gitzense/locker/pics/billet_2.jpg

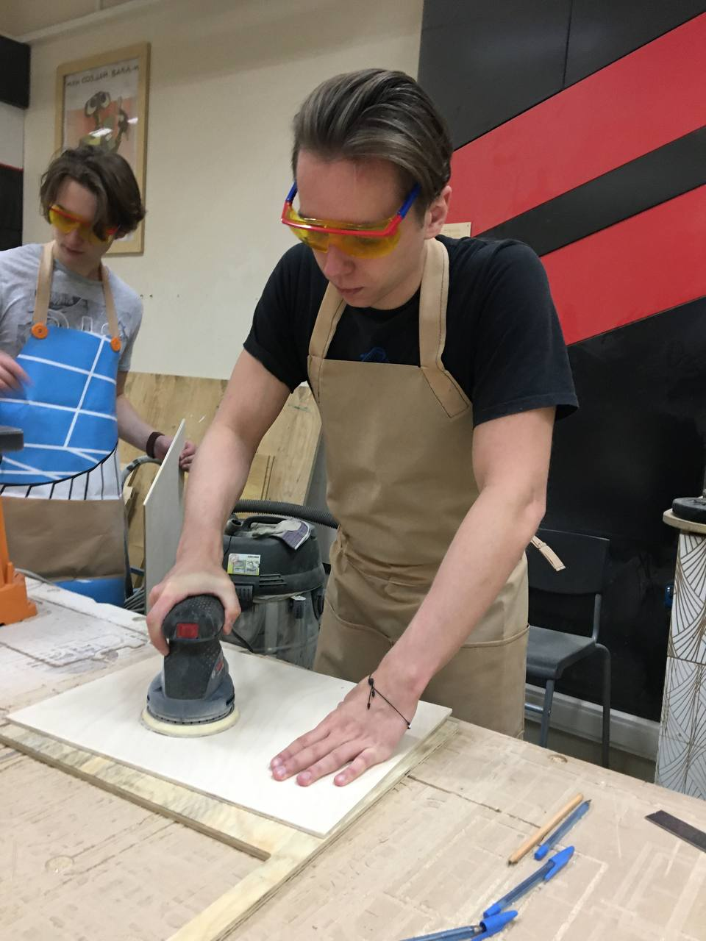
pics/billet_2.jpg
