gitzense/locker/pics/billet_3.jpg

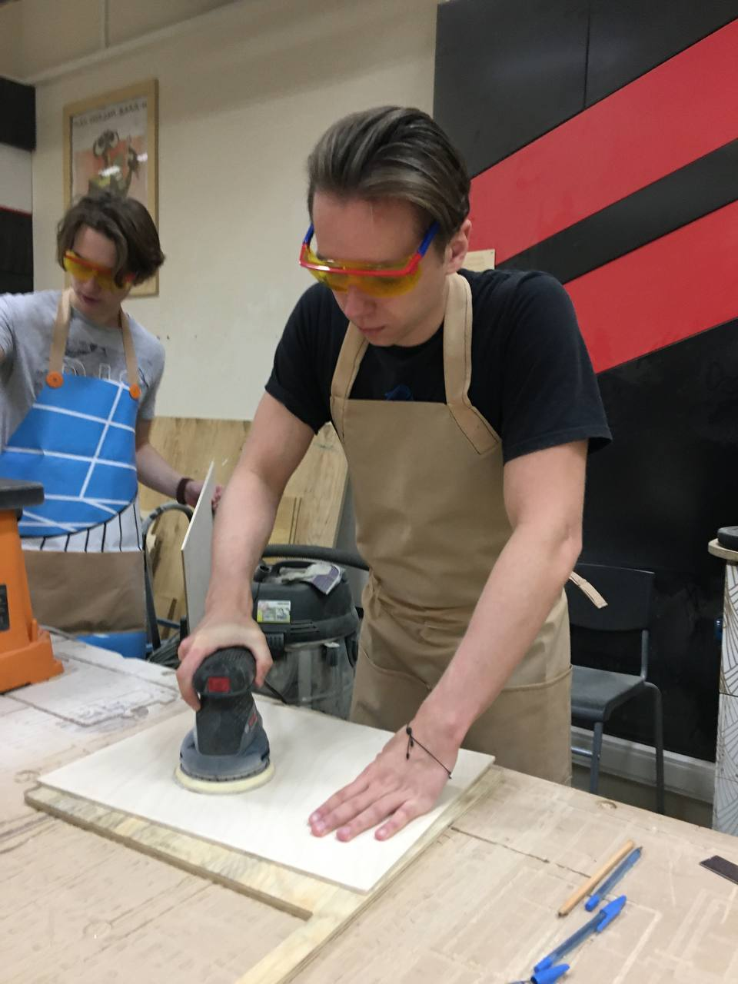
pics/billet_3.jpg
