gitzense/locker/pics/billet_4.jpg

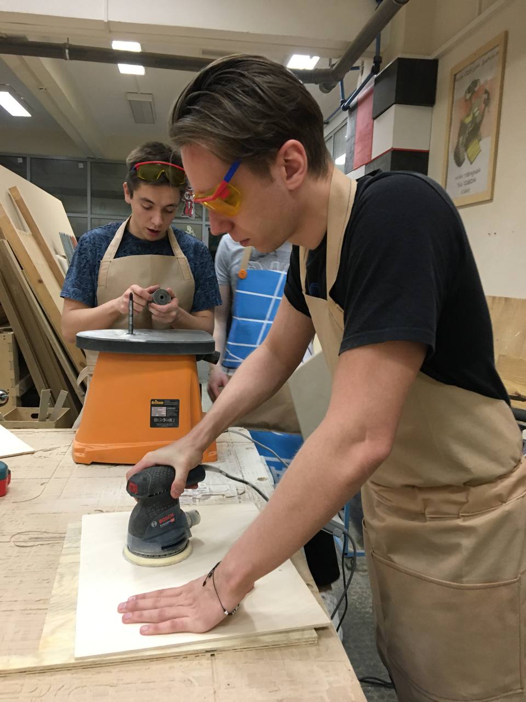
pics/billet_4.jpg
