gitzense/locker/pics/billet_5.jpg

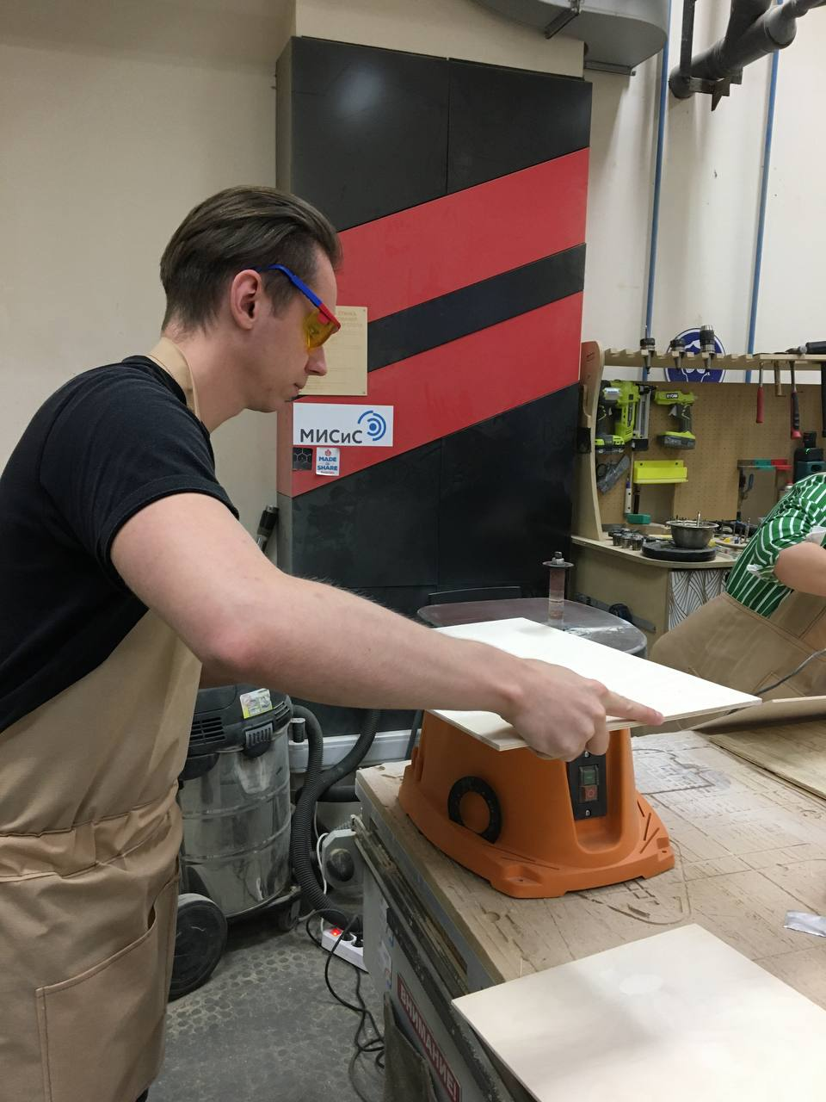
pics/billet_5.jpg
