gitzense/locker/pics/billet_7.jpg

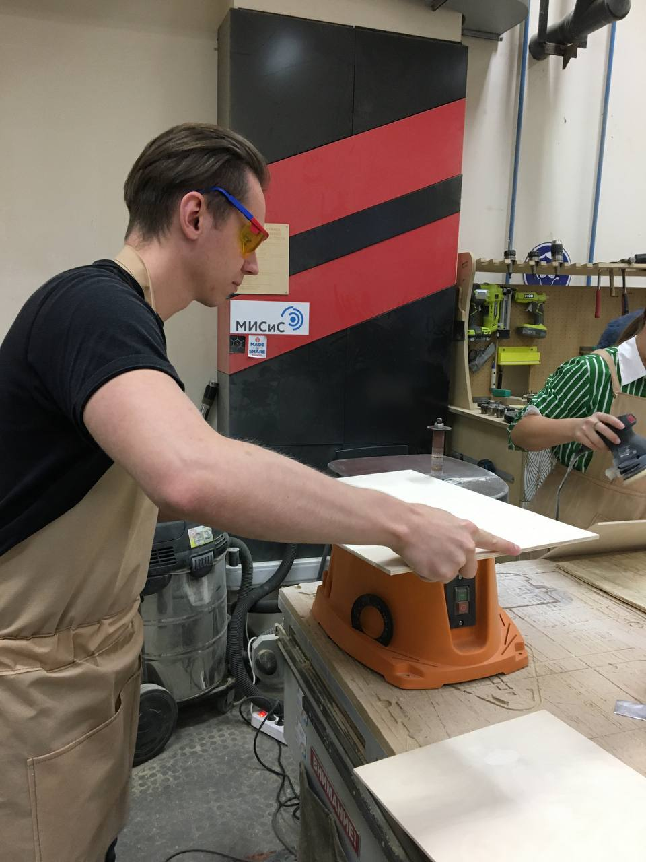
pics/billet_7.jpg
