gitzense/locker/pics/card 1.jpg

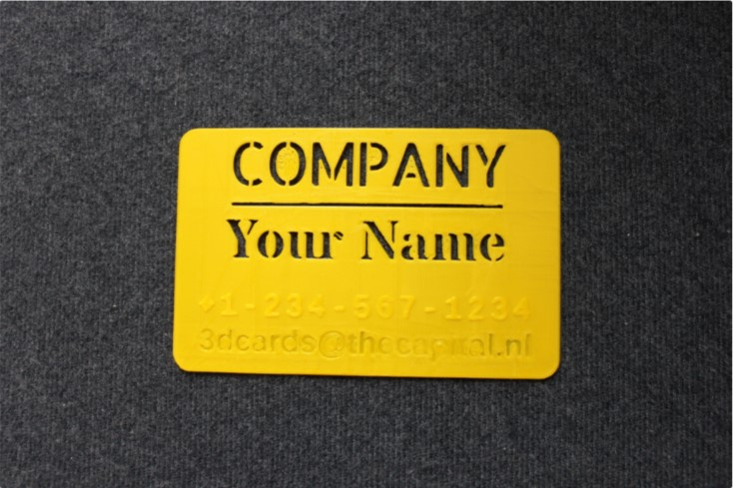
pics/card 1.jpg
