gitzense/locker/pics/card 2.jpg

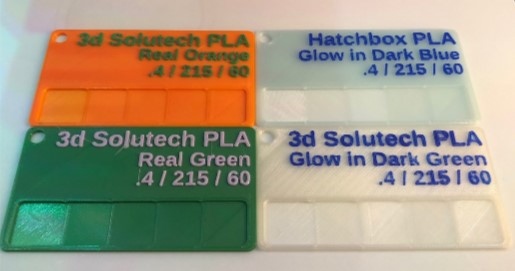
pics/card 2.jpg
