gitzense/locker/pics/card_done_1.jpg

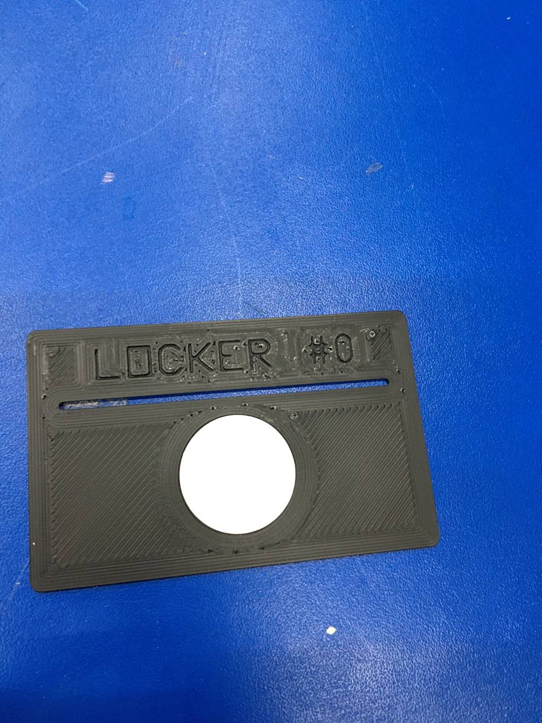
pics/card_done_1.jpg
