gitzense/locker/pics/card_done_2.jpg

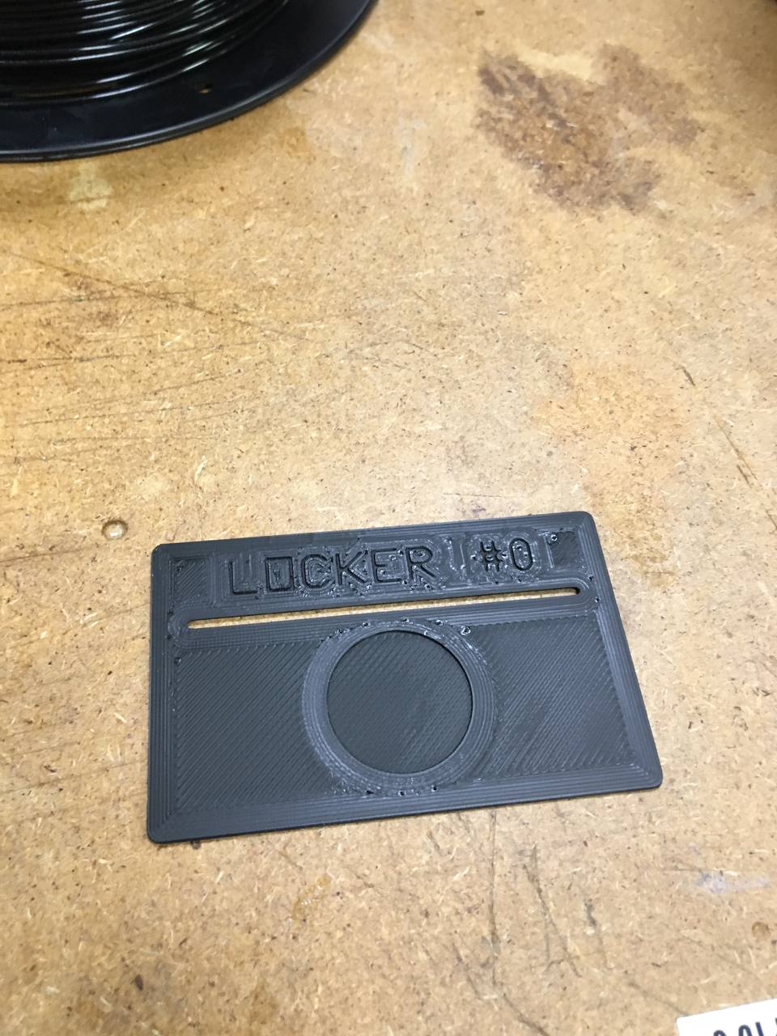
pics/card_done_2.jpg
