gitzense/locker/pics/card_rfid_diam.jpg

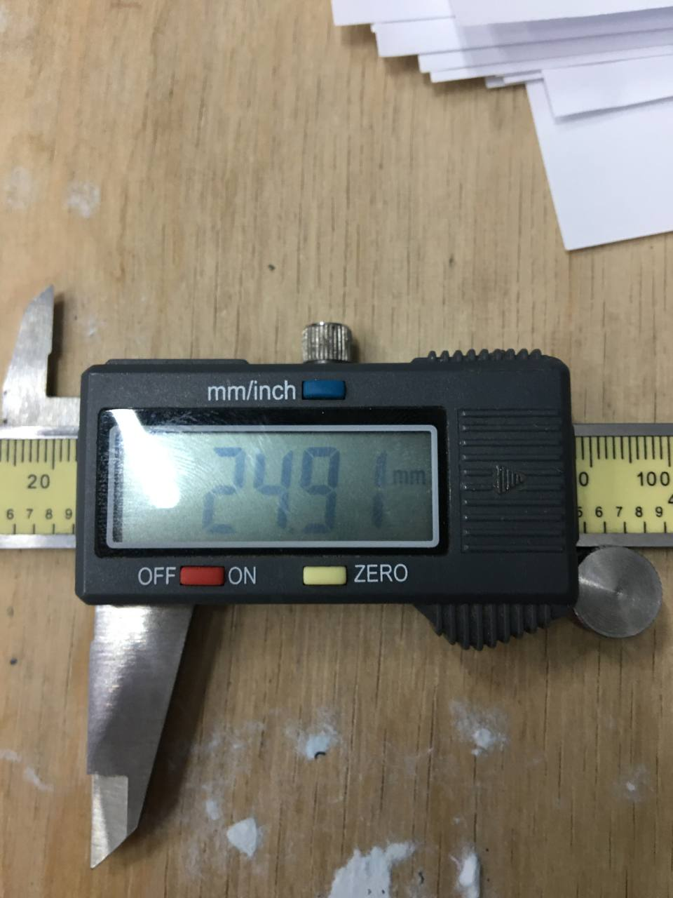
pics/card_rfid_diam.jpg
