gitzense/locker/pics/card_sketch.jpg

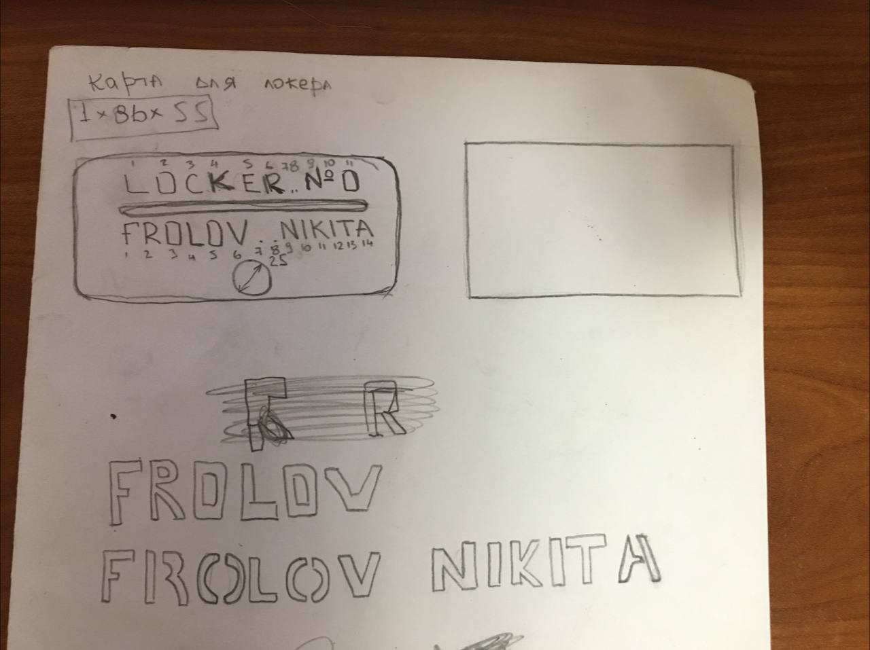
pics/card_sketch.jpg
