gitzense/locker/pics/card_slicer.jpg

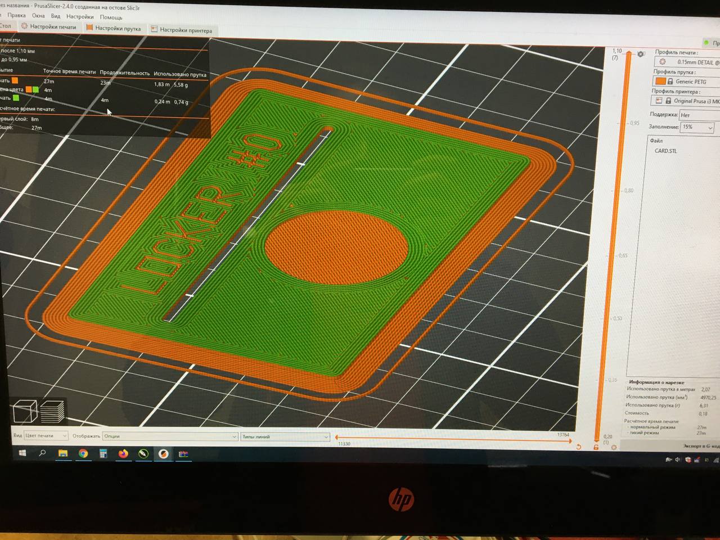
pics/card_slicer.jpg
