gitzense/locker/pics/door_hinge_in_process.jpg

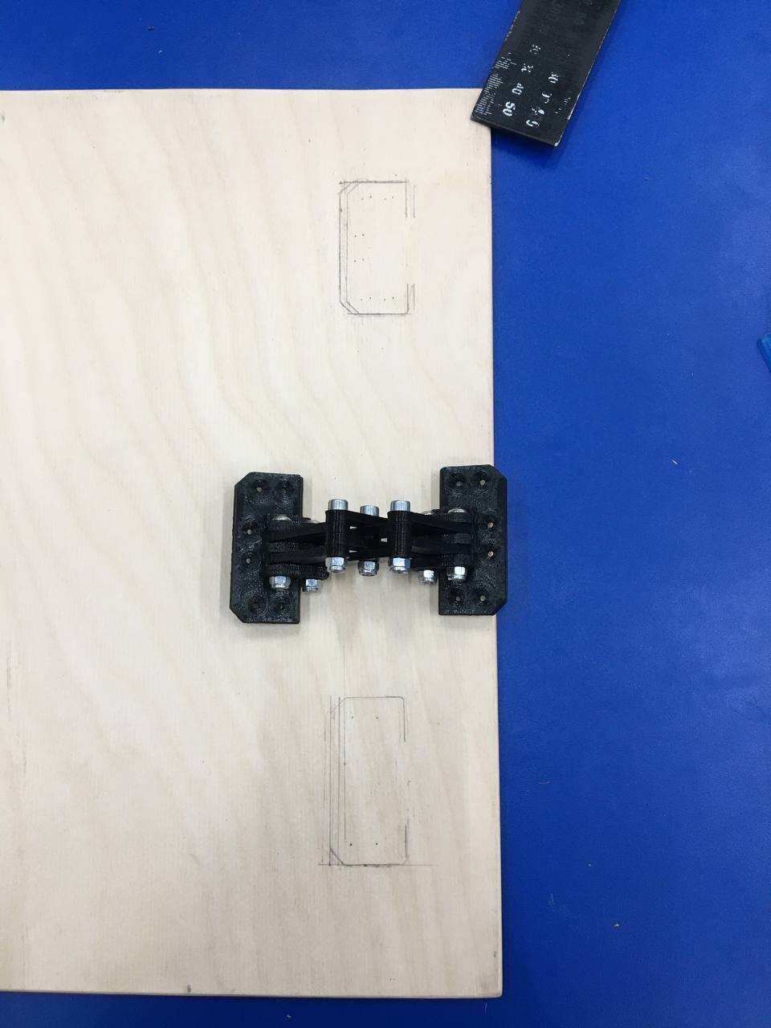
pics/door_hinge_in_process.jpg
