gitzense/locker/pics/door_hinge_in_process_2.jpg

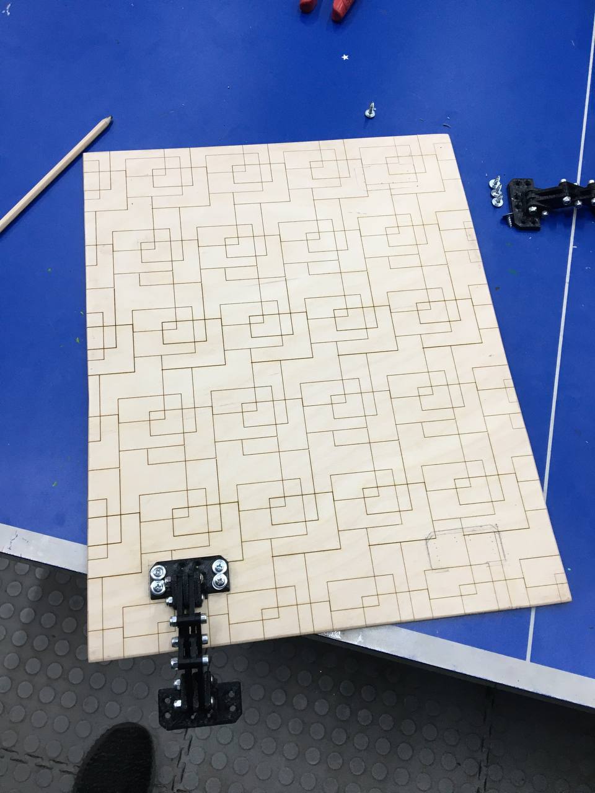
pics/door_hinge_in_process_2.jpg
