gitzense/locker/pics/hinge.jpg

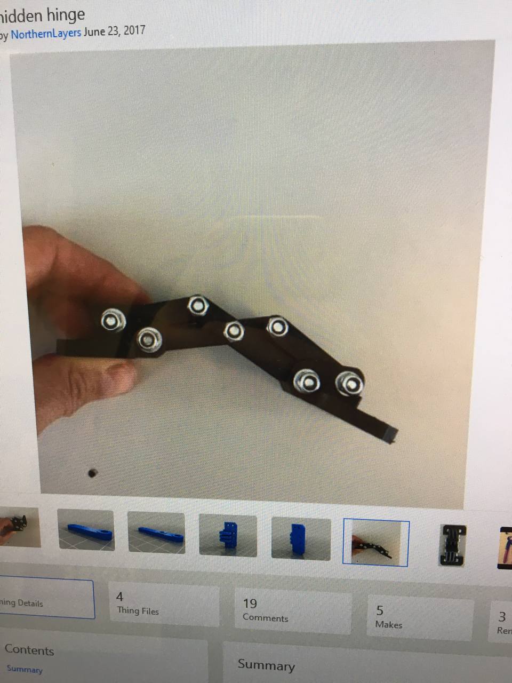
pics/hinge.jpg
