gitzense/locker/pics/hinge_done_1.jpg

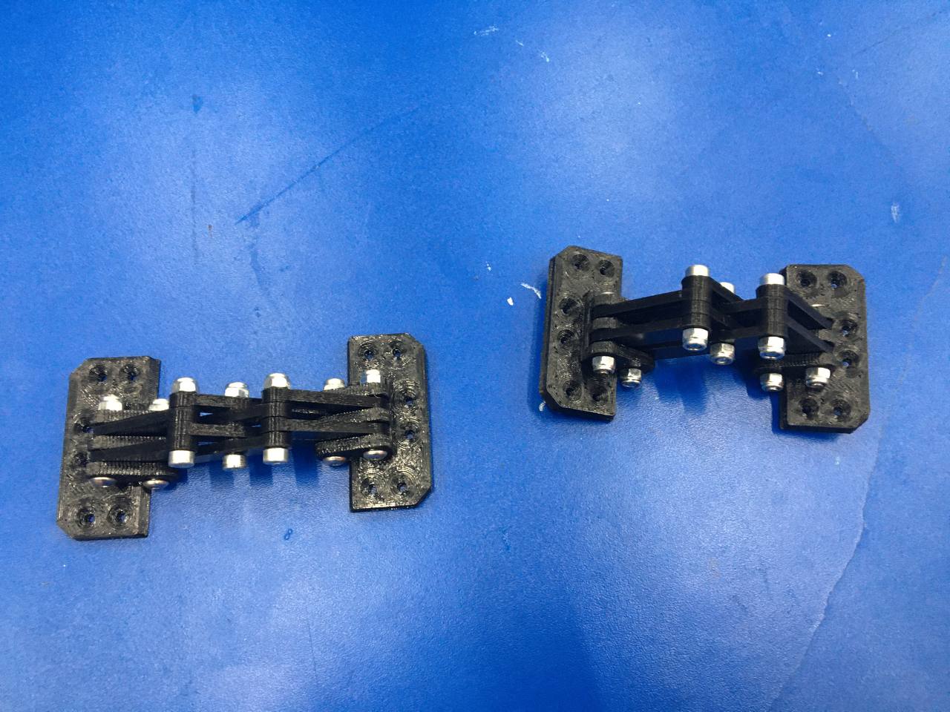
pics/hinge_done_1.jpg
