gitzense/locker/pics/hinge_done_2.jpg

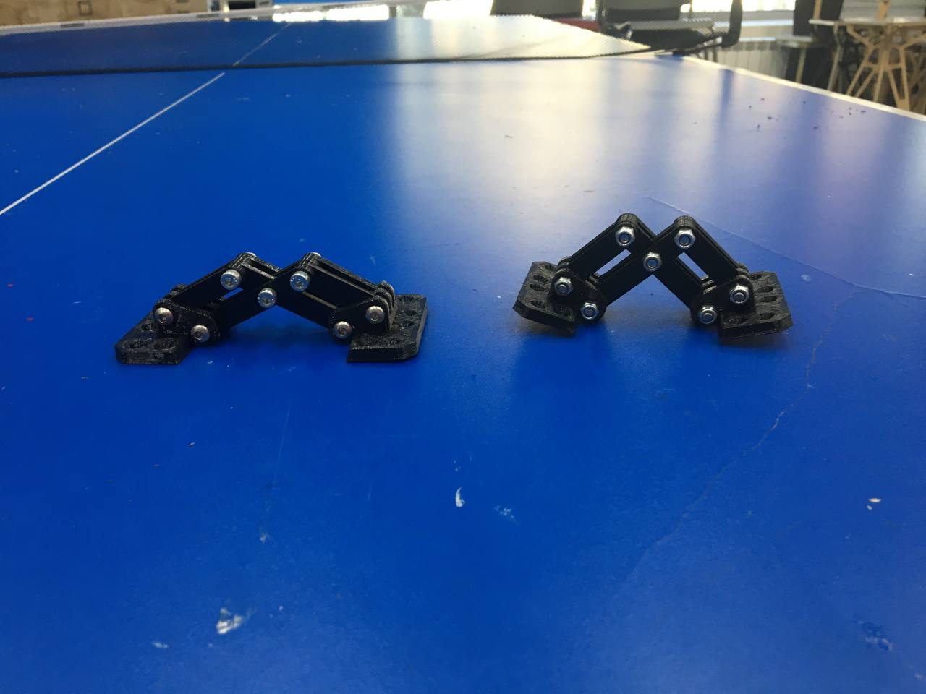
pics/hinge_done_2.jpg
