gitzense/locker/pics/hinge_done_3.jpg

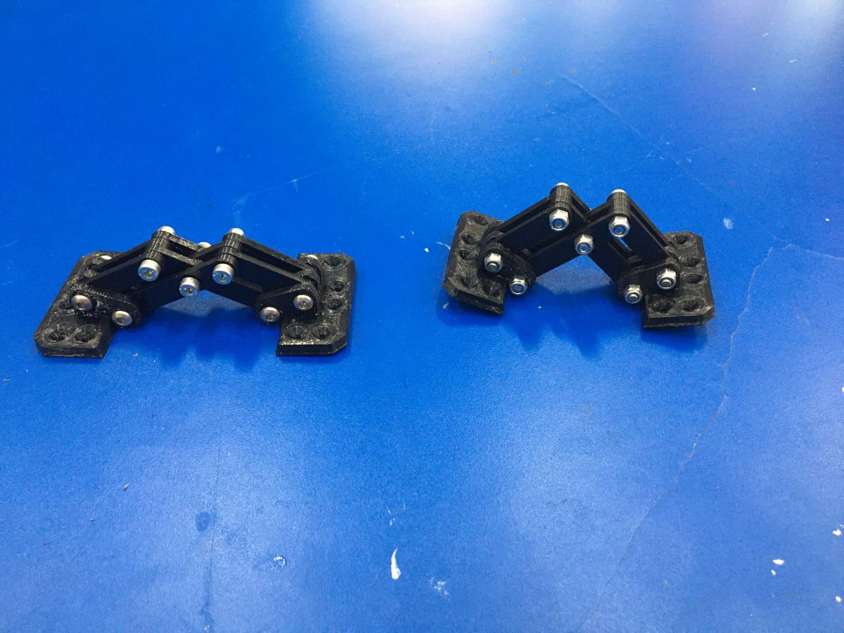
pics/hinge_done_3.jpg
