gitzense/locker/pics/hinge_done_4.jpg

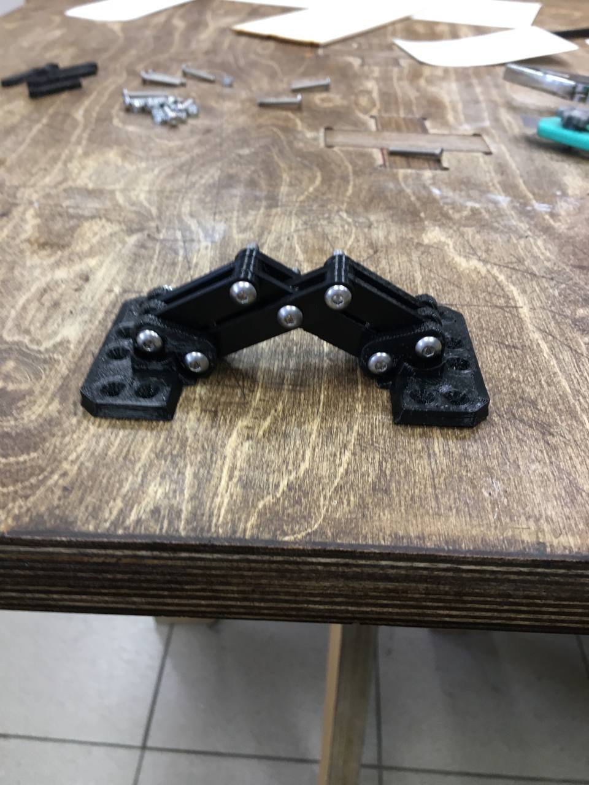
pics/hinge_done_4.jpg
