gitzense/locker/pics/hinge_done_5.jpg

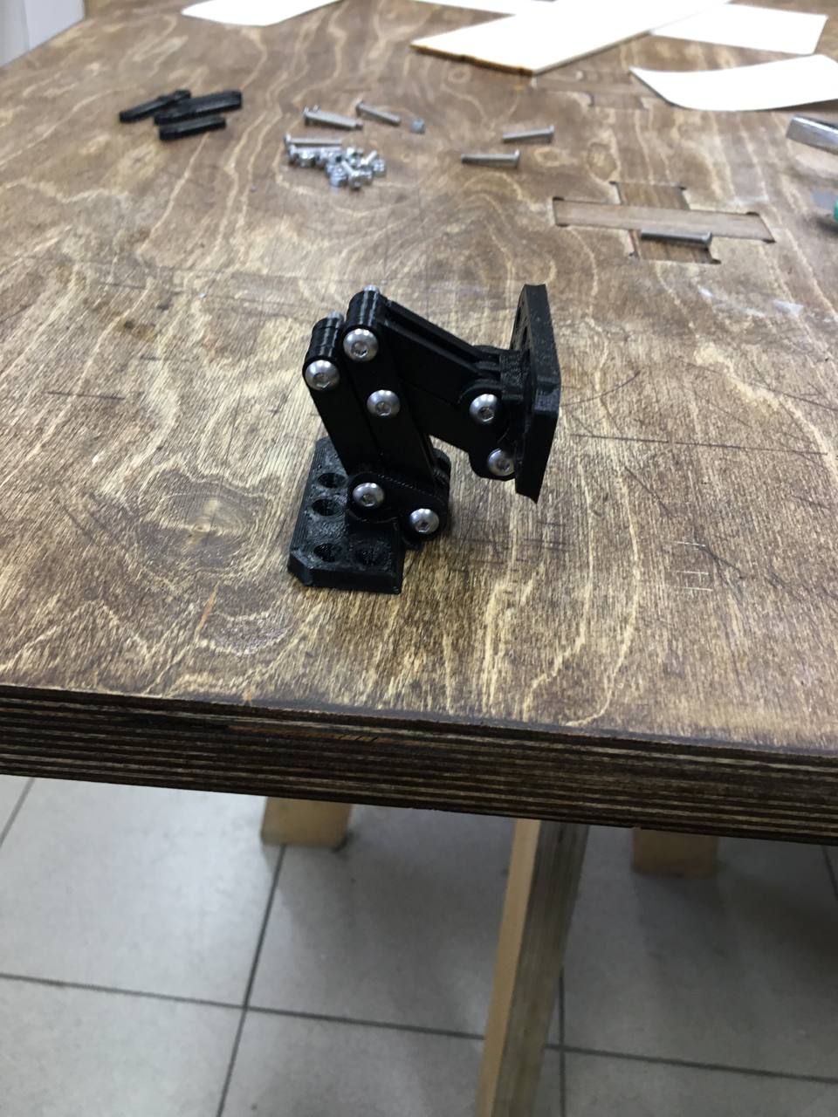
pics/hinge_done_5.jpg
