gitzense/locker/pics/hinge_fail_1.jpg

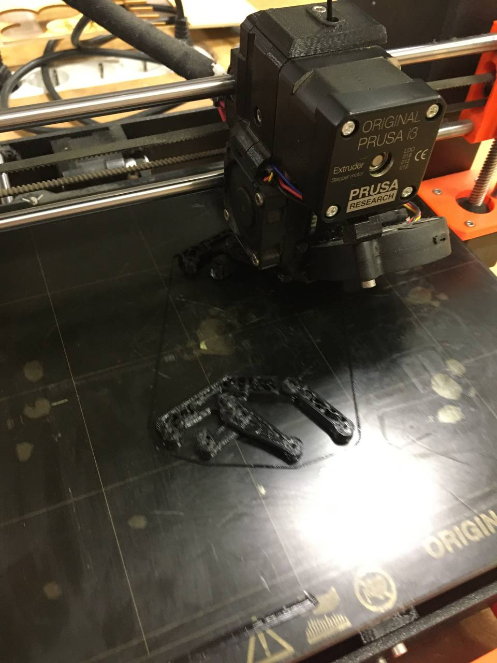
pics/hinge_fail_1.jpg
