gitzense/locker/pics/hinge_fail_2.jpg

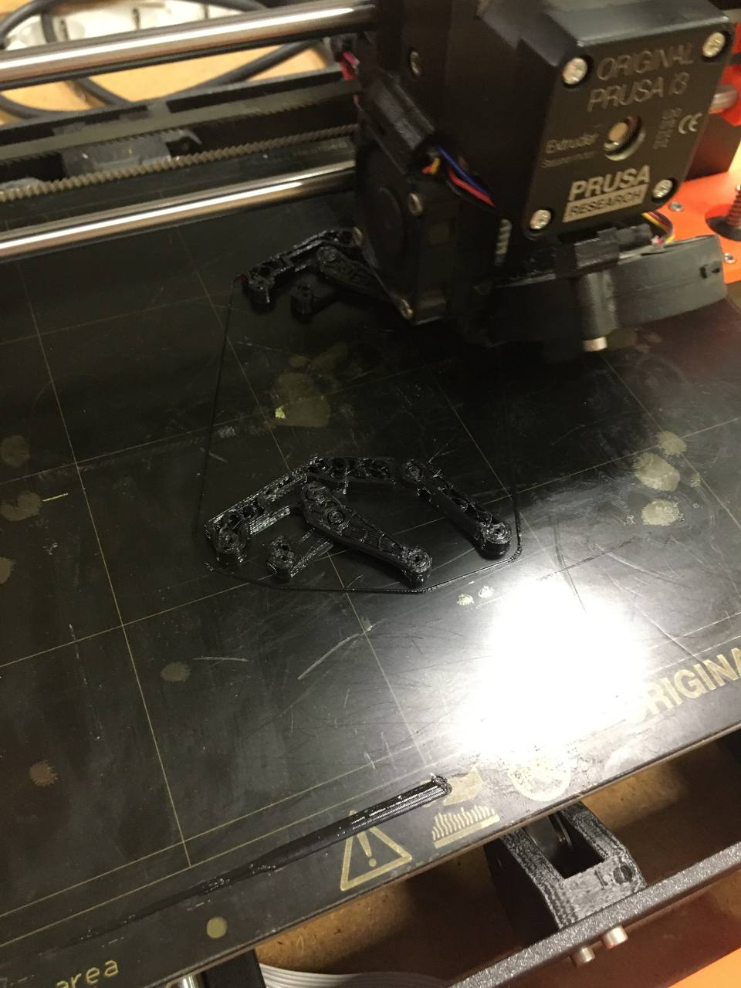
pics/hinge_fail_2.jpg
