gitzense/locker/pics/laser point.jpg

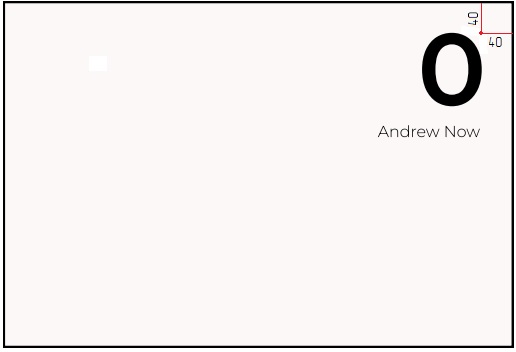
pics/laser point.jpg
