gitzense/locker/pics/lock_blocker_done.jpg

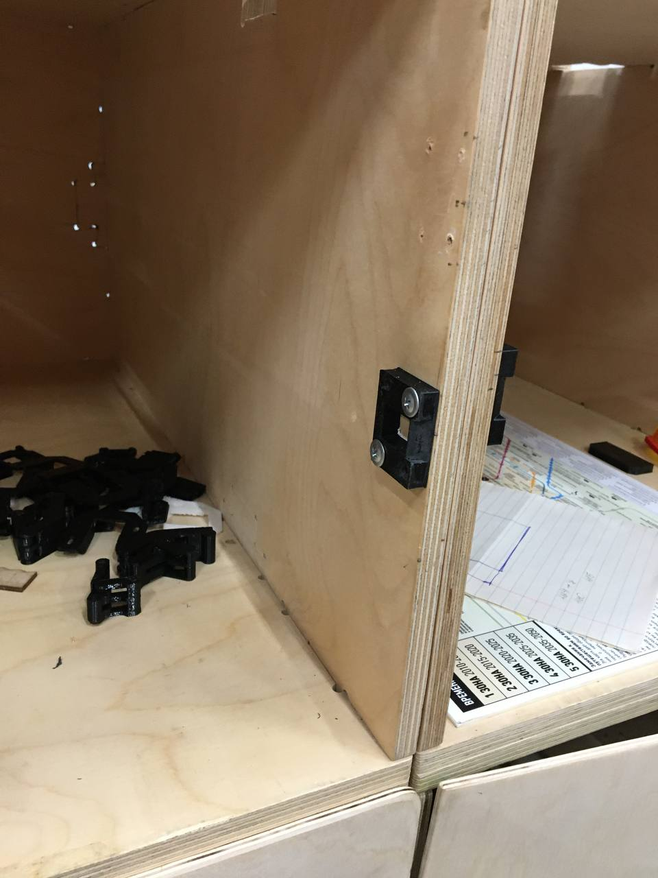
pics/lock_blocker_done.jpg
