gitzense/locker/pics/number_and_name_laser_1.jpg

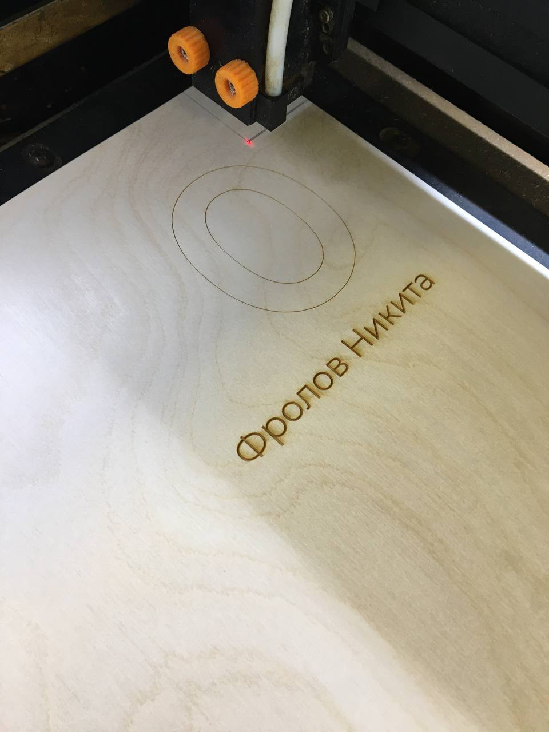
pics/number_and_name_laser_1.jpg
