gitzense/locker/pics/number_and_name_laser_2.jpg

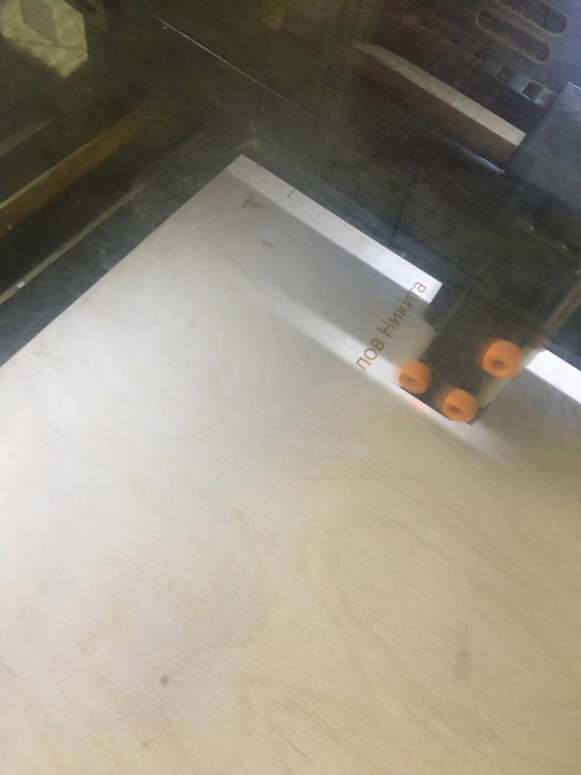
pics/number_and_name_laser_2.jpg
