gitzense/locker/pics/number_paint.jpg

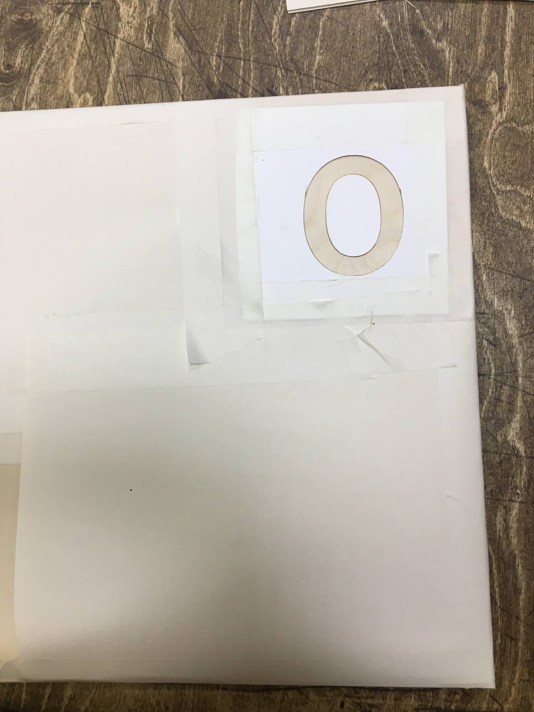
pics/number_paint.jpg
