gitzense/locker/pics/pattern.jpg

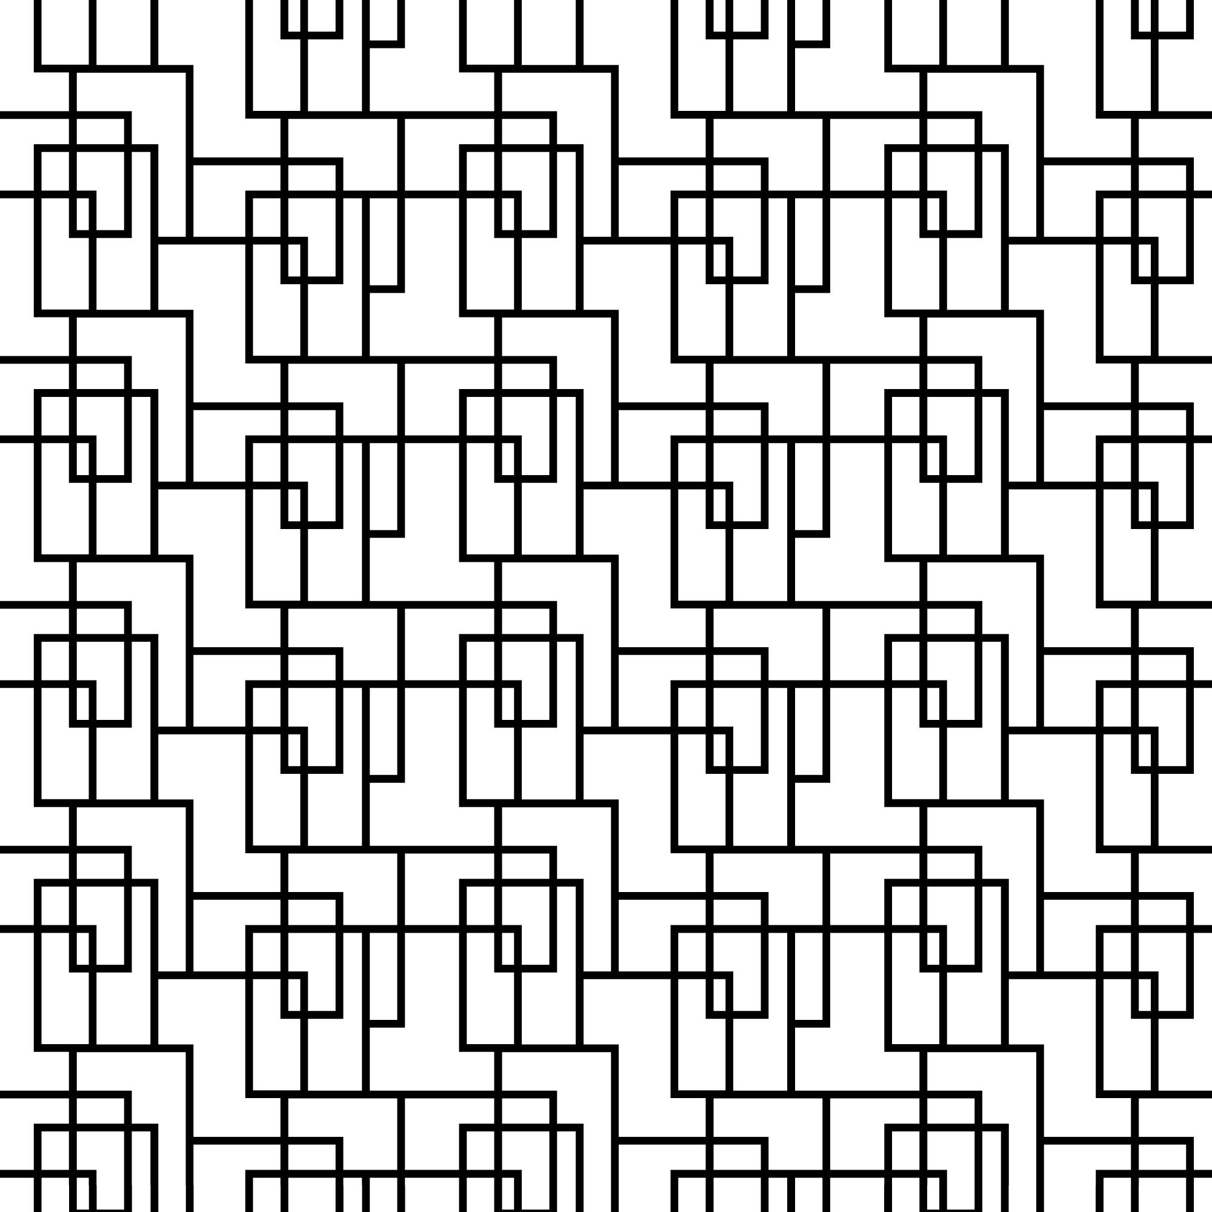
pics/pattern.jpg
