gitzense/locker/pics/pattern_done_1.jpg

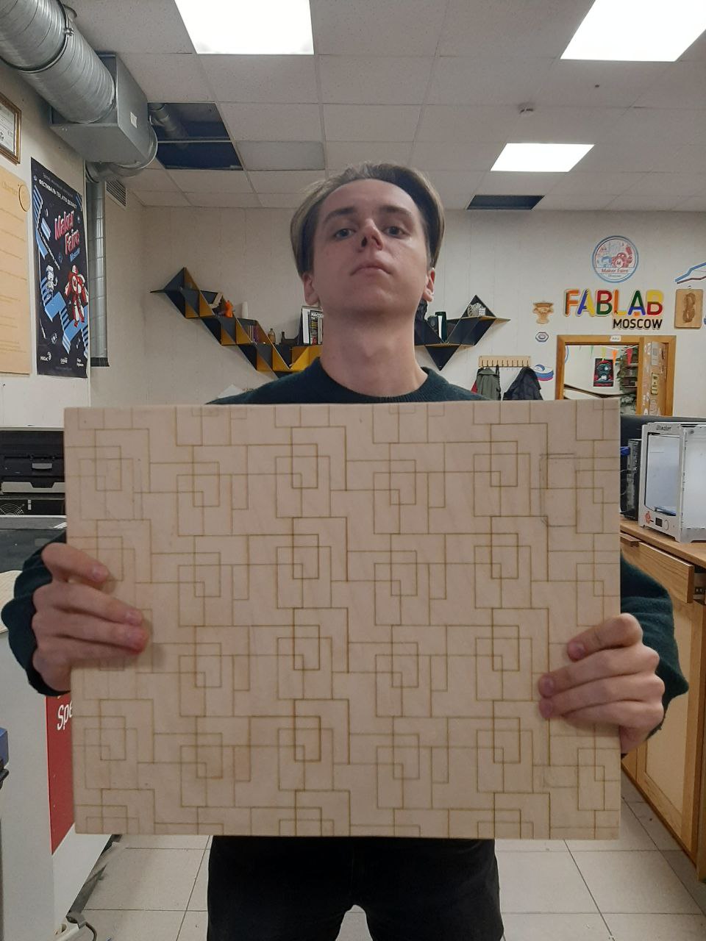
pics/pattern_done_1.jpg
