gitzense/locker/pics/pattern_done_2.jpg

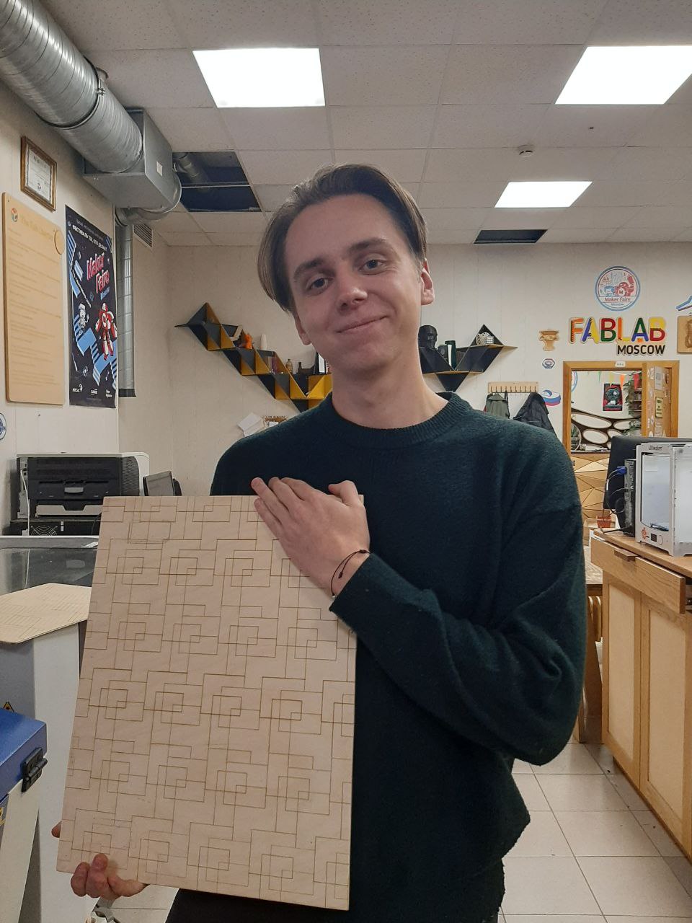
pics/pattern_done_2.jpg
