gitzense/locker/pics/pattern_in_process_1.jpg

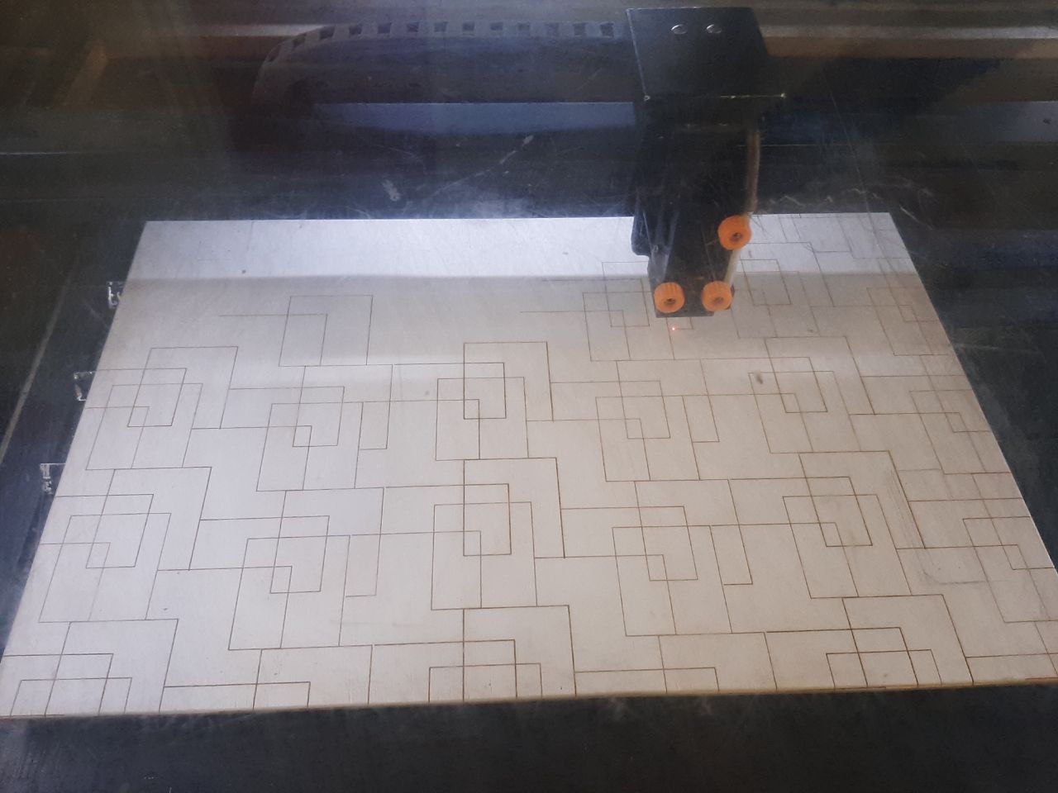
pics/pattern_in_process_1.jpg
