gitzense/locker/pics/pattern_in_process_2.jpg

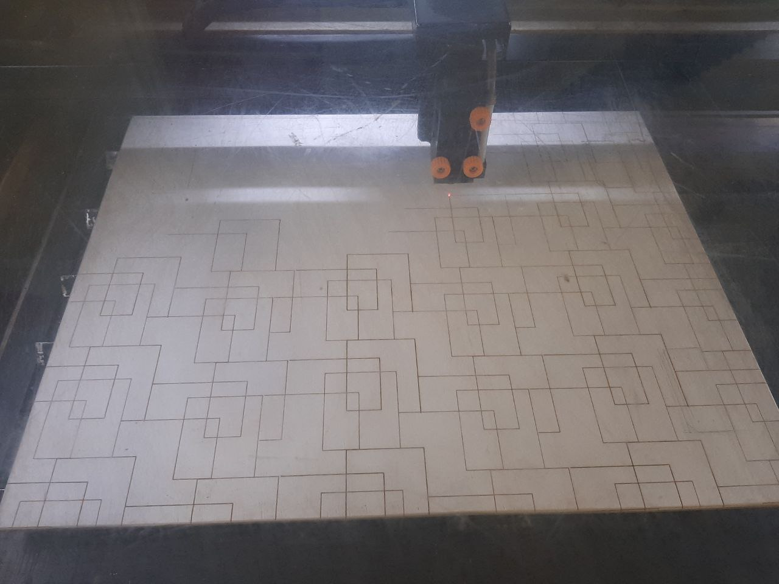
pics/pattern_in_process_2.jpg
