gitzense/locker/pics/pattern_in_process_3.jpg

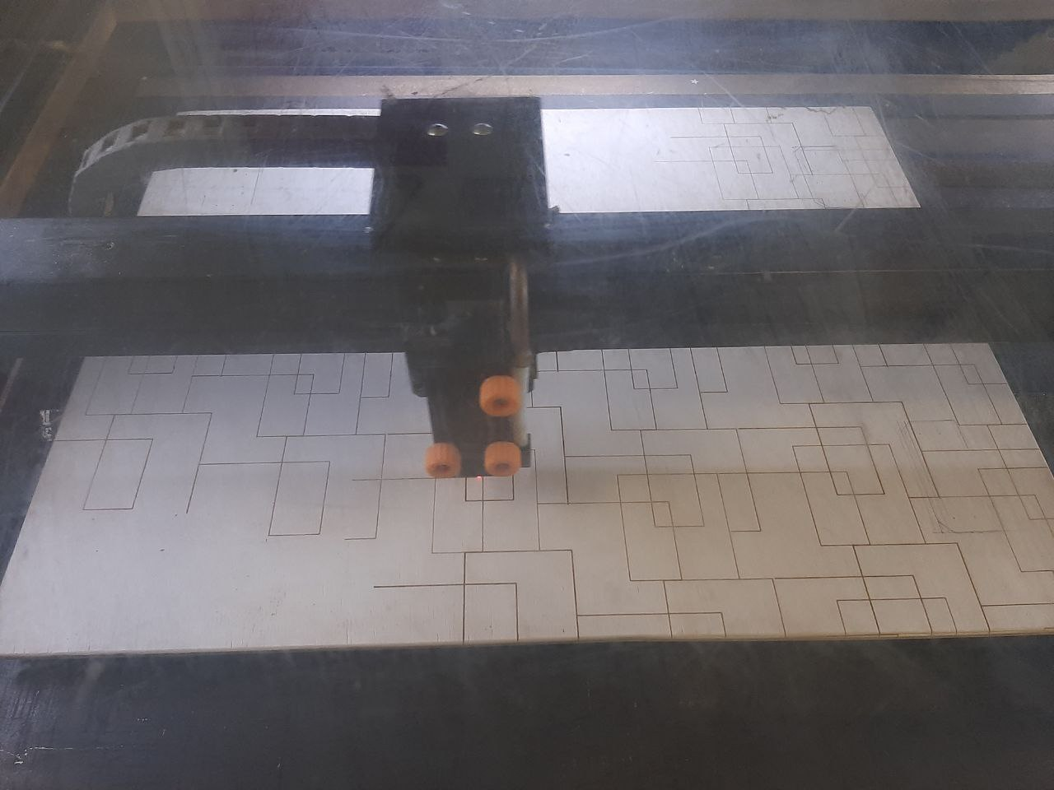
pics/pattern_in_process_3.jpg
