gitzense/locker/pics/solenoid_done_1.jpg

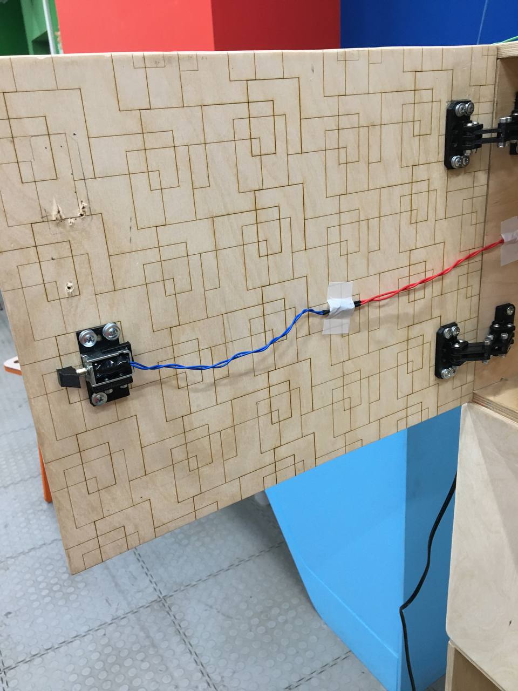
pics/solenoid_done_1.jpg
