gitzense/locker/pics/solenoid_in_process_1.jpg

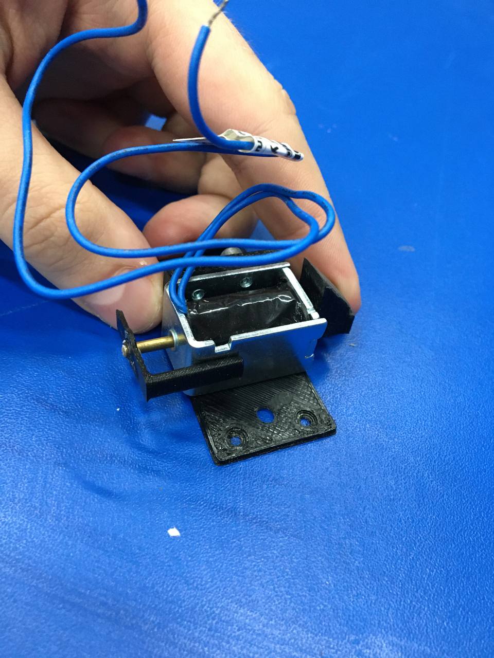
pics/solenoid_in_process_1.jpg
