gitzense/locker/pics/wires_1.jpg

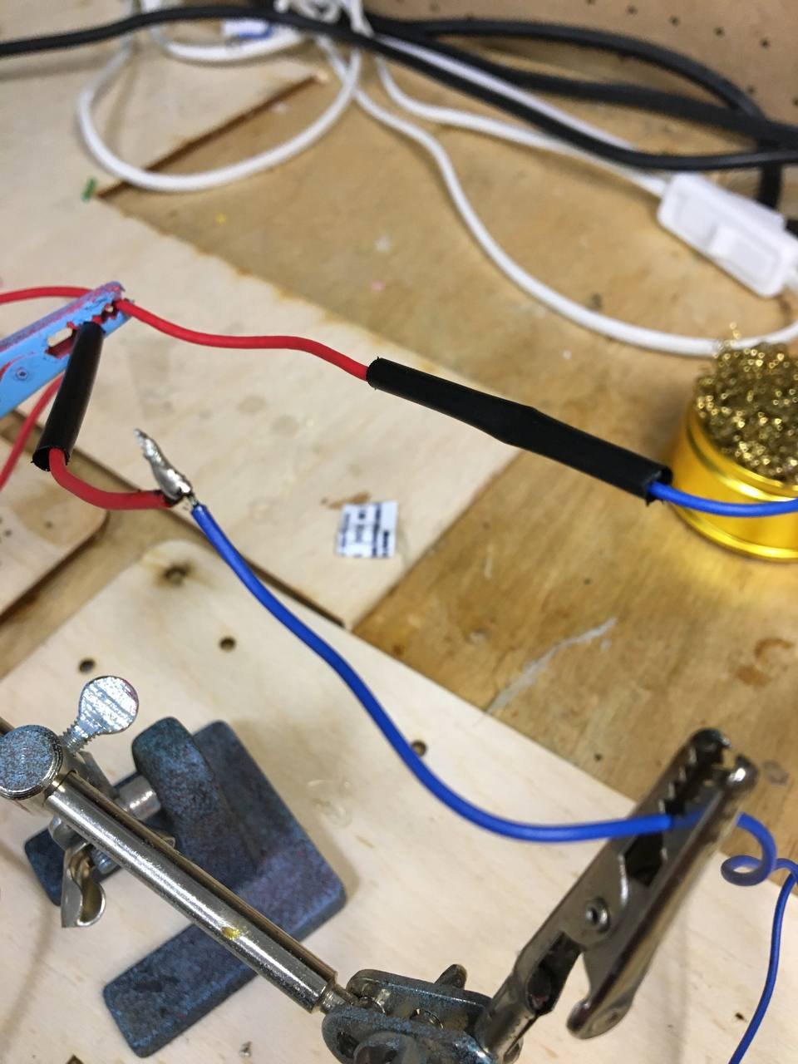
pics/wires_1.jpg
