gitzense/locker/pics/wires_2.jpg

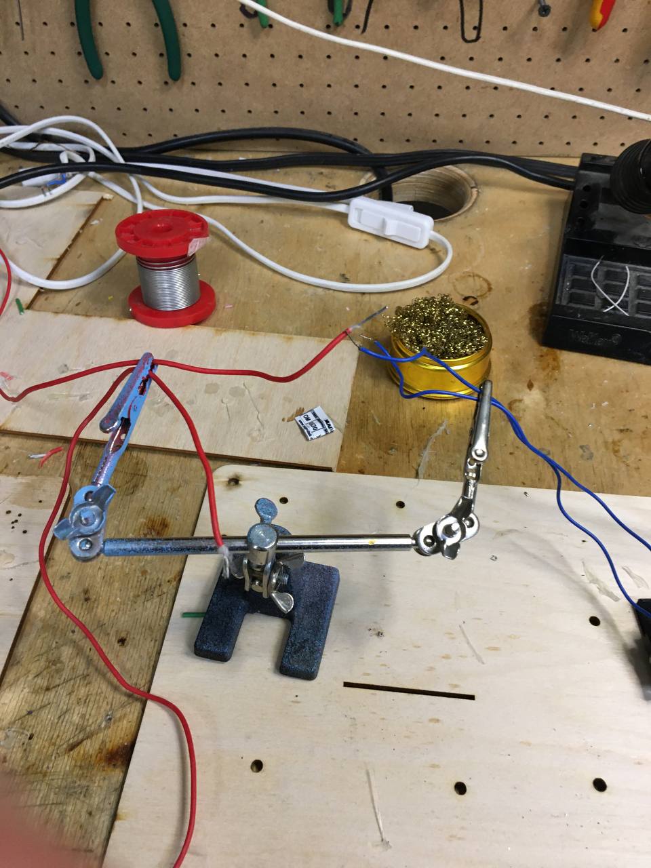
pics/wires_2.jpg
