gitzense/locker/pics/wires_3.jpg

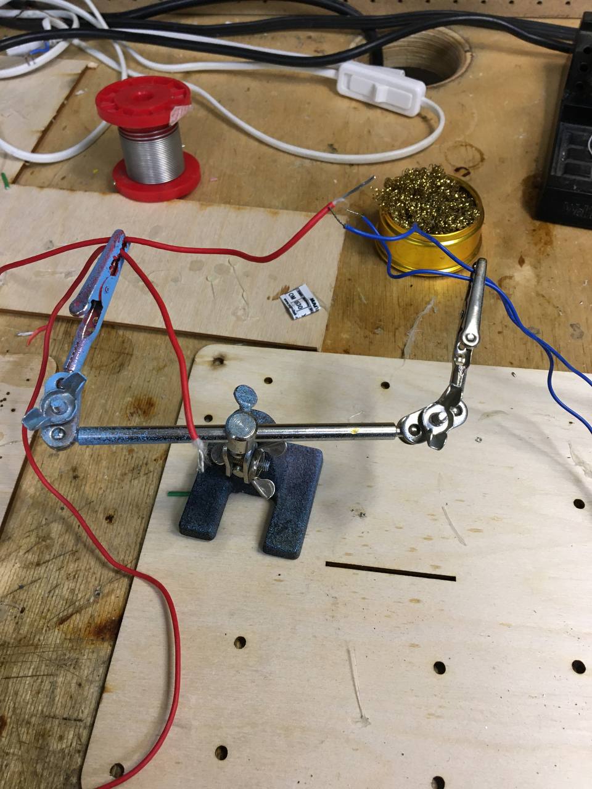
pics/wires_3.jpg
