gitzense/locker/pics/final_result_1.jpg

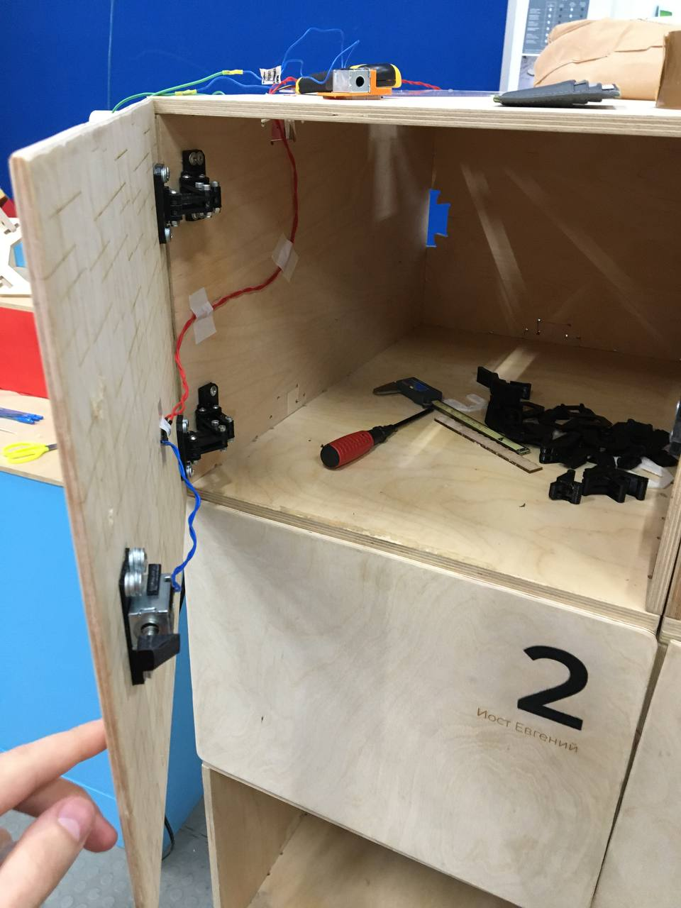
pics/final_result_1.jpg
