gitzense/locker/pics/final_result_2.jpg

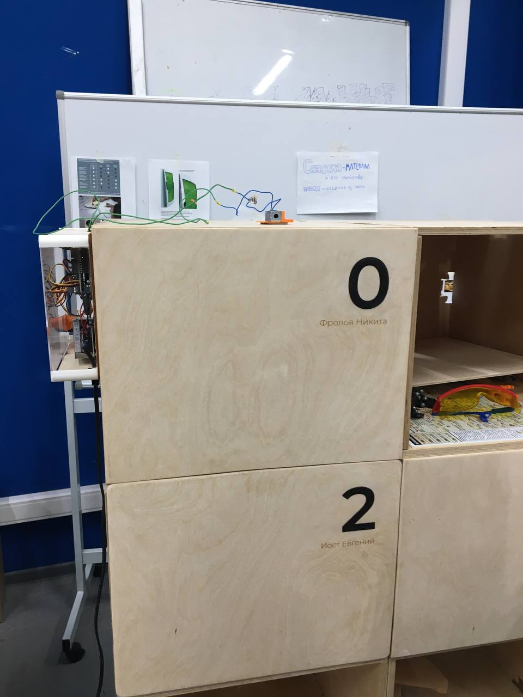
pics/final_result_2.jpg
